neomura/console/shell/foot-measurements.scad

function console_foot_diameter() = 9.5;
function console_foot_margin() = 5;
function console_foot_protrusion() = 3;
function console_foot_embed() = 1;
function console_foot_sides() = 128;
function console_foot_tolerance() = 0.5;
