neomura/console/shell/label-measurements.scad

function console_label_width() = 41;
function console_label_height() = 31;
function console_label_radius() = 2;
