neomura/console/shell/led-measurements.scad

use <button-measurements.scad>;

function console_led_width() = 2.125;
function console_led_length() = 5.125;

function console_led_positions() = [
  [
    0,
    -13,
    90,
  ],
];
