neomura/console/shell/resistor-measurements.scad

function console_resistor_width() = 3;
function console_resistor_height() = 3;
function console_resistor_length() = 12.26;

function console_resistor_positions() = [
  [0, -17, 90],
];
