neomura/console/shell/slot-measurements.scad

use <pad-connector-measurements.scad>;

function console_slot_x() = 0;
function console_slot_y() = -1;
